Elecrow-RD/CrowPanel-Advanced-10.1inch-ESP32-P4-HMI-AI-Display-1024x600-IPS-Touch-Screen/example/V1.0/idf-code/7_9_10.1_P4_HMI_AI/readme.md

## P4 HMI AI Demo User Guide

#### Preparation tools:

P4 HMI display (different screens correspond to different code, except for the code, all other operation steps are the same)



#### USB cable:



#### VS Code (ESP-IDF v5.4.2 installed)



Download the code for the corresponding screen size:

CrowPanel Advanced 10.1 inch | ESP32-P4 HMI AI Display:
https://drive.google.com/drive/folders/1ShJZmeXBA-P1ATnCS_sbFRyz8KRpYGxG?usp=sharing

Use VS Code to open the project (here we take the 9-inch screen as an example, the operation steps are the same for other sizes):

##### 1. Open VS Code and choose to open the project folder.



##### 2. Select the folder you want to open, click “Select Folder” to open the project. Be careful not to double-click to open it.



##### 3. Connect the device to the computer. Connect the device side to the UART0 port and plug it into the computer’s COM port.



##### 4. Before compiling, we need to modify the Wi-Fi account and password in the code to the ones that can currently connect (choose a 2.4G network): find main -> boards -> elecrow-p4-board -> elecrow_board.cc, and in lines 334–350, change all “elecrow888” to the Wi-Fi name you want to connect to. Change all “elecrow2014” to the Wi-Fi password you want to use.



Assume the Wi-Fi name you need to change to is: wifiP4, and the password is: 12345678, then modify it as follows:



##### 5. Select ESP-IDF v5.4.2.



##### 6. Select the flashing method.



##### 7. Select the COM port.



##### 8. Select the flashing development board – esp32p4.



##### 9. Before flashing, you can choose to clear the previous “build” cache. This step is not necessary, but you can choose to clear it. If you have modified the code, clearing the previous cache will improve the compilation success rate.



##### 10. Compile the project. Please make sure the network connection is good. The compilation process may take some time, so please wait patiently.



This means the compilation is successful:



##### 11. Click to flash to the P4 HMI development board.



##### 12. After flashing is completed, when the device connects to Wi-Fi, the screen will display the verification code for connecting the device:



##### 13. On the computer, log in to the “xiaozhi.me” website to configure the device, and first set it to the English version.



##### 14. Click “Console” to enter the console.



##### 15. Click “Add Device” to add a device.



##### 16. Enter the device code, then click “Confirm”. Note that the device code here must be based on the output displayed on your own device.



##### 17. Select “Open Source” and click “Start Using”.



##### 18. Now your AI device can already chat. Since the default language is Chinese, we also need to configure the role. Click “Configure Role”.



##### 19. Set “Dialogue Language” to “English”.



##### 20. Save the configuration.



##### 21. Next, we set the wake word. First, go back to “Agents”.



##### 22. Select “Manage Devices”.



##### 23. Select “Customize”, then choose “English”, and click “Next” to enter the next configuration step.



##### 24. In “Select Wake Word”, choose your wake word, or you can select “No Wake Word” if you do not want a wake word.

Note: Here you can also choose to customize the emojis you need by selecting “Emoji Collection”. Otherwise, there will be no emojis. You also need to select a preset font; otherwise, the dialogue text will not be fully displayed.



##### 25. After selecting, click “Next”.



##### 26. Click “Generate assets.bin”.



##### 27. Start Generate.



##### 28. Click “Flash to Device Online” to perform the remote update. After the update is completed, you can use the new wake word to wake up the device.



##### 29. During the update process, please do not disconnect the device from power or the network.
