Elecrow-RD/CrowPanel-Advanced-10.1inch-ESP32-P4-HMI-AI-Display-1024x600-IPS-Touch-Screen/example/V1.2/AI_Conversation/7inch_9inch_10inch_P4_HMI_AI/docs/v1/electron-bot.png

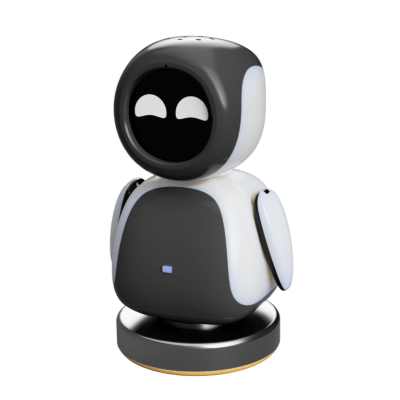
example/V1.2/AI_Conversation/7inch_9inch_10inch_P4_HMI_AI/docs/v1/electron-bot.png
