Elecrow-RD/CrowPanel-Advanced-10.1inch-ESP32-P4-HMI-AI-Display-1024x600-IPS-Touch-Screen/example/V1.2/Squareline_Studio/image/table_lamp400.png

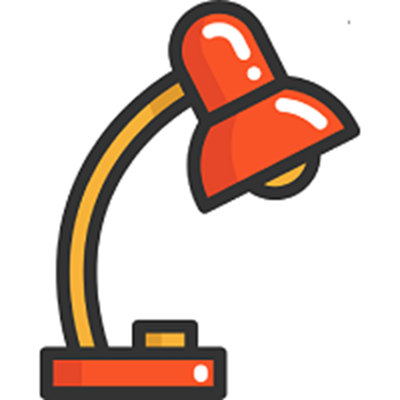
example/V1.2/Squareline_Studio/image/table_lamp400.png
