Elecrow-RD/CrowPanel-Advanced-10.1inch-ESP32-P4-HMI-AI-Display-1024x600-IPS-Touch-Screen/factory_firmware/V1.1_and_V1.2/ESP32P4_10.1 factory firmware/P4-UI_Firmware download address.png

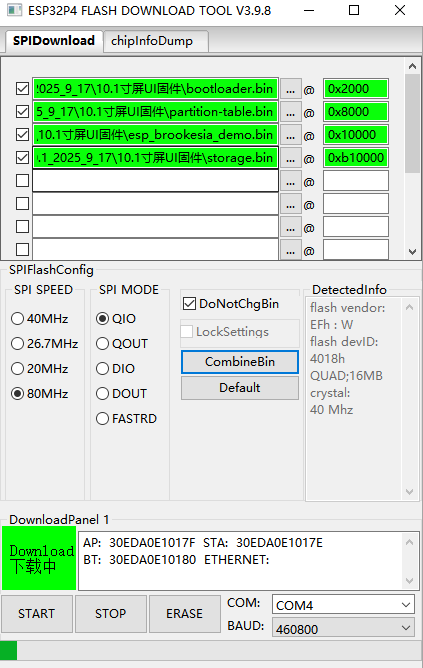
factory_firmware/V1.1_and_V1.2/ESP32P4_10.1 factory firmware/P4-UI_Firmware download address.png
