Elecrow-RD/CrowPanel-Advanced-10.1inch-ESP32-P4-HMI-AI-Display-1024x600-IPS-Touch-Screen/example/CrowPanel_Advance_ESP32-P4 Display_Firmware_Upgrade_Guide/Advance_P4_On-Board_ESP32C6_Firmware_V2.12.3_2026_04_08/ESP32C6_Firmware_Download_Address.png

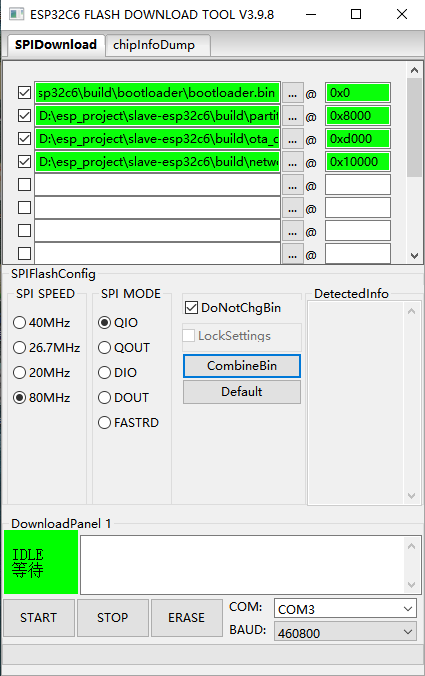
example/CrowPanel_Advance_ESP32-P4 Display_Firmware_Upgrade_Guide/Advance_P4_On-Board_ESP32C6_Firmware_V2.12.3_2026_04_08/ESP32C6_Firmware_Download_Address.png
